shortcircuitaudio/loopy-docs/pcb.20210224/DSCF1690.jpg

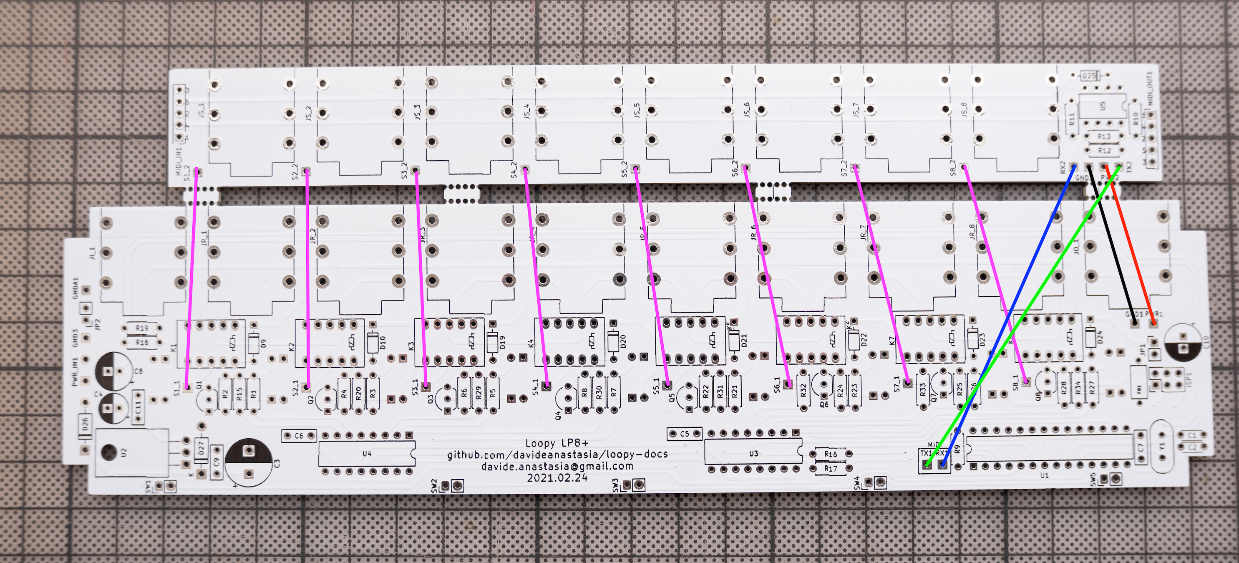
pcb.20210224/DSCF1690.jpg
