shortcircuitaudio/loopy-docs/pcb.20210226/DSCF1692.jpg

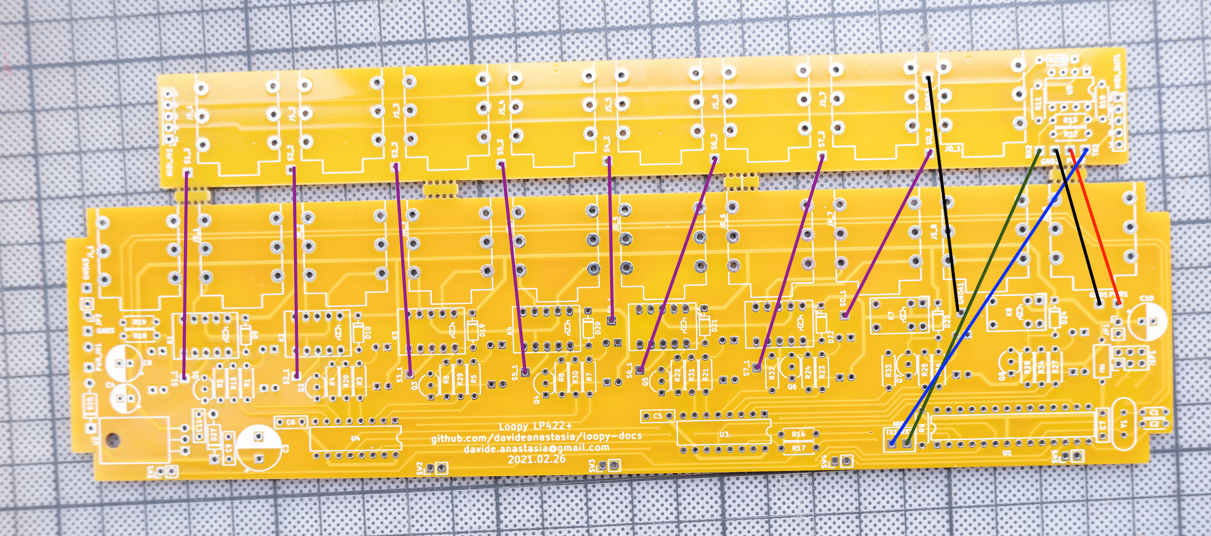
pcb.20210226/DSCF1692.jpg
